LaviniaTudor003/TSC_proiect/Images/Screenshot 2025-04-06 223841.png

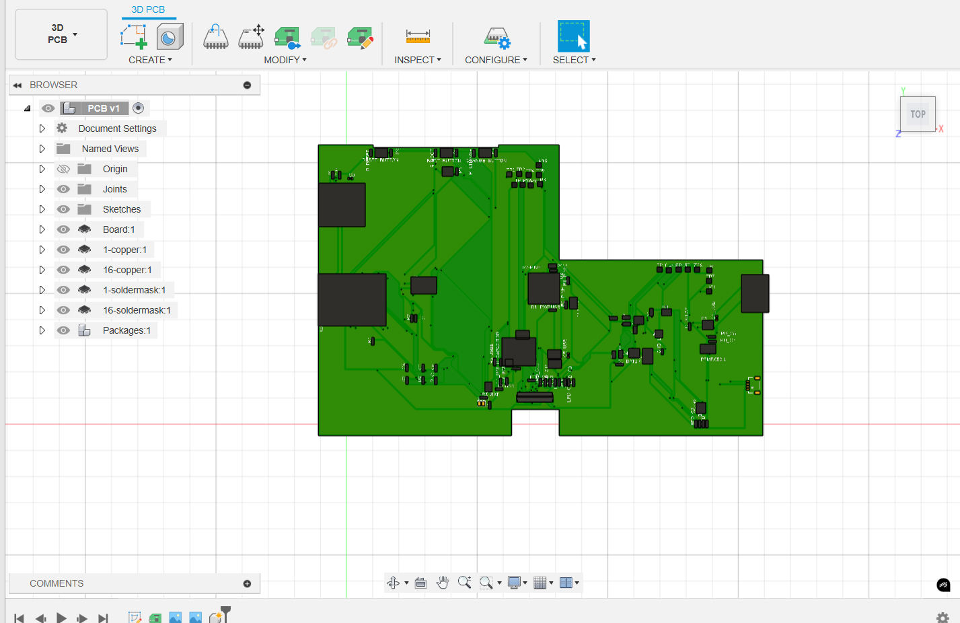
Images/Screenshot 2025-04-06 223841.png
