LaviniaTudor003/TSC_proiect/Images/Screenshot 2025-04-14 131421.png

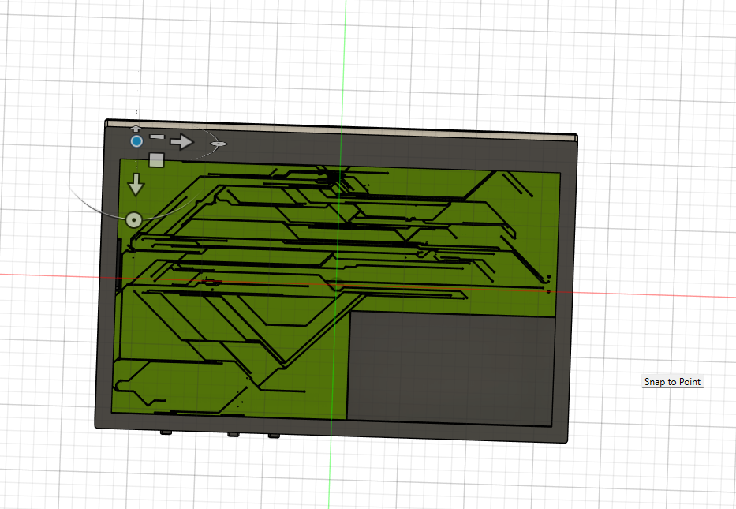
Images/Screenshot 2025-04-14 131421.png
