LaviniaTudor003/TSC_proiect/Images/Screenshot 2025-04-14 134929.png

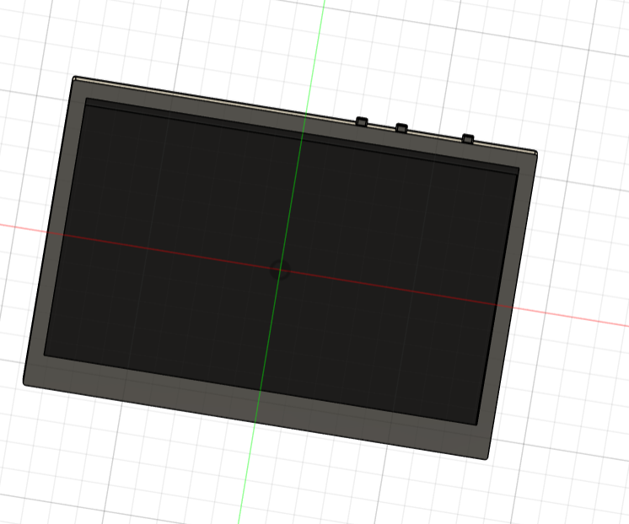
Images/Screenshot 2025-04-14 134929.png
