LaviniaTudor003/TSC_proiect/Images/Screenshot 2025-04-14 160136.png

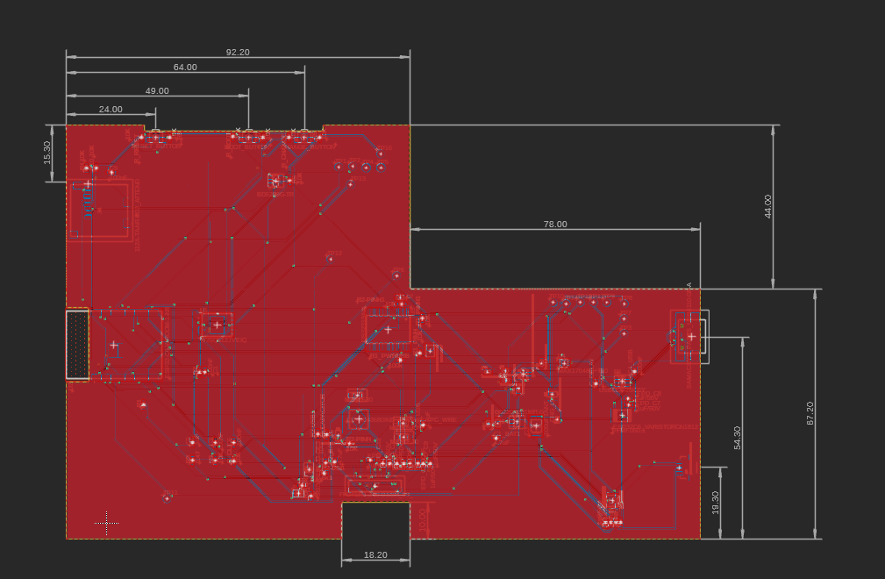
Images/Screenshot 2025-04-14 160136.png
